SeanCline/RabidKeyboard/pcb/images/pcb-back-3d.png

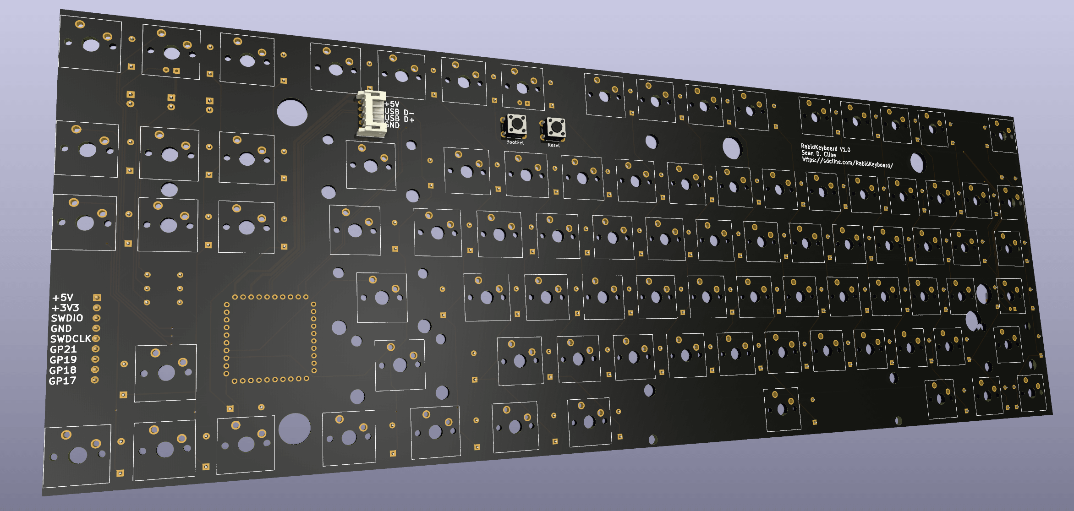
pcb/images/pcb-back-3d.png
