SeanCline/RabidKeyboard/pcb/images/pcb-back.png

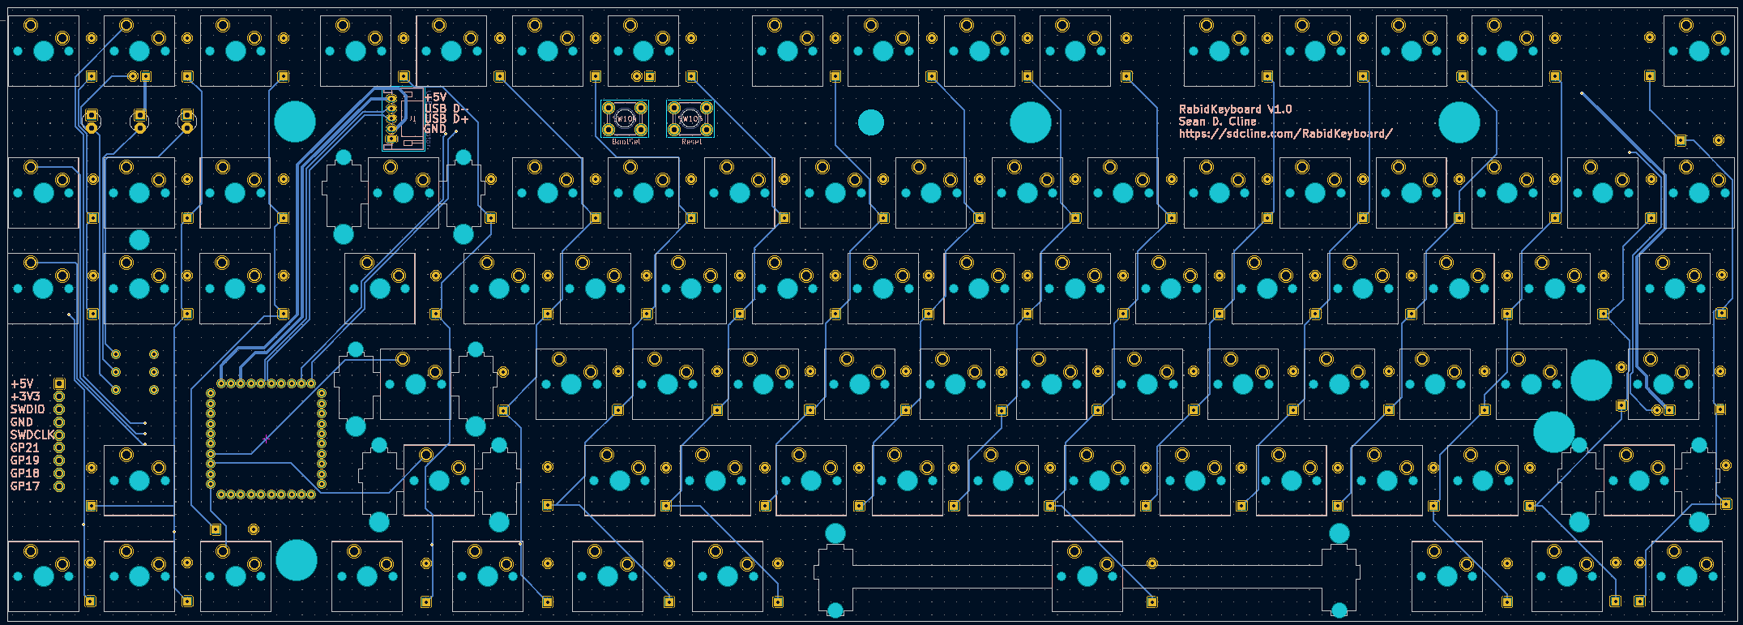
pcb/images/pcb-back.png
