SeanCline/RabidKeyboard/plate/images/plate-front.png

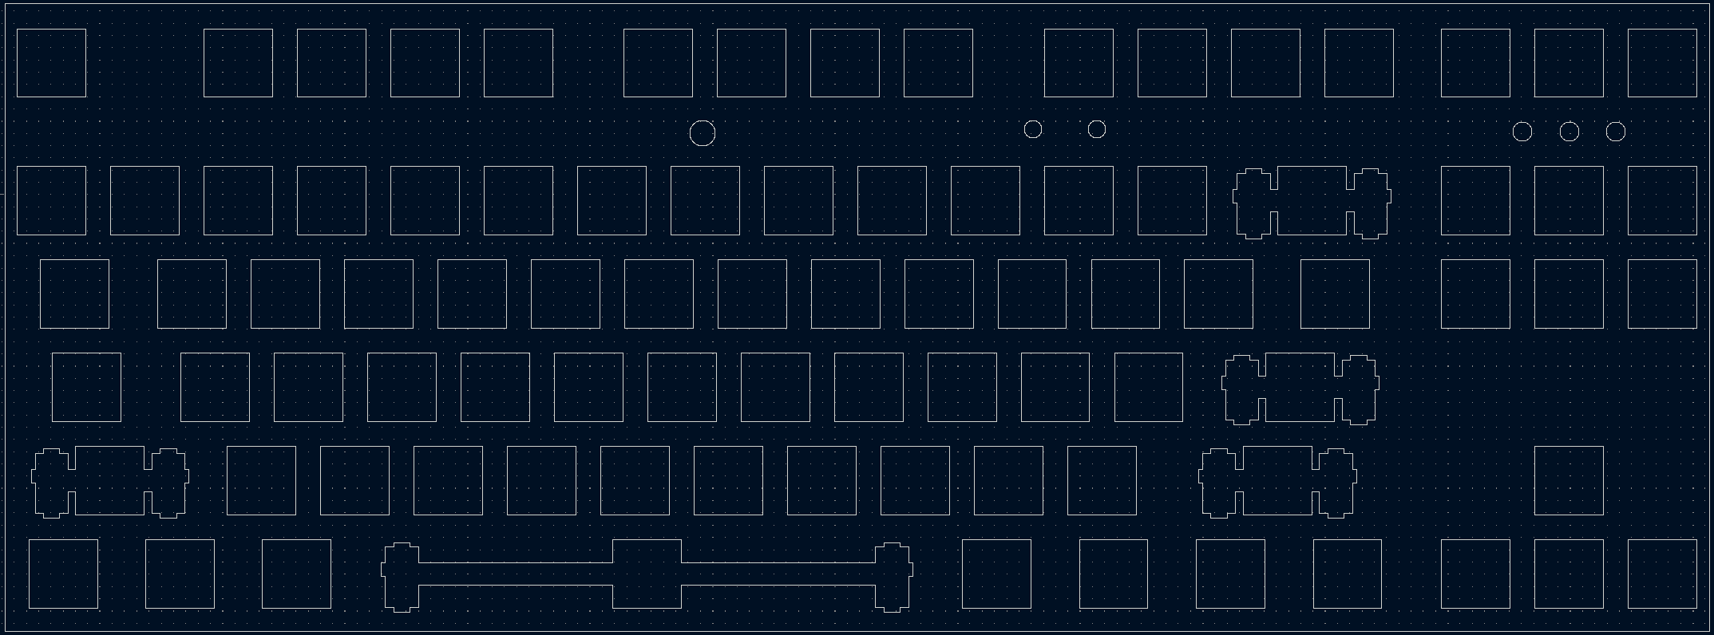
plate/images/plate-front.png
