SeanCline/RabidKeyboard/reference/Microcontrollers/pga2040.jpg

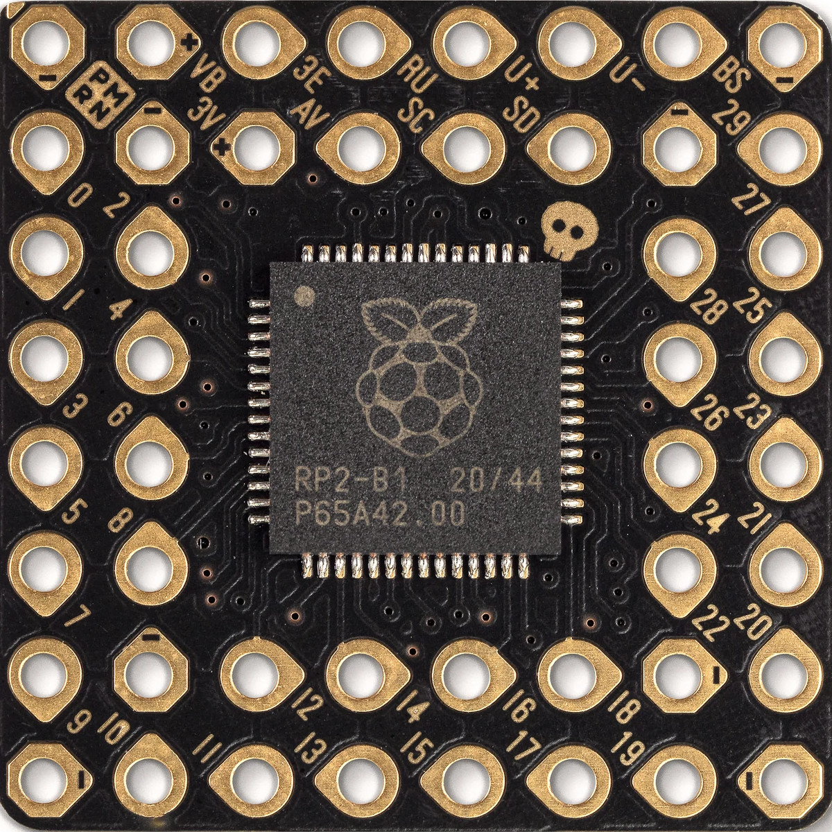
reference/Microcontrollers/pga2040.jpg
