SeanCline/RabidKeyboard/reference/Microcontrollers/pi_pico.jpg

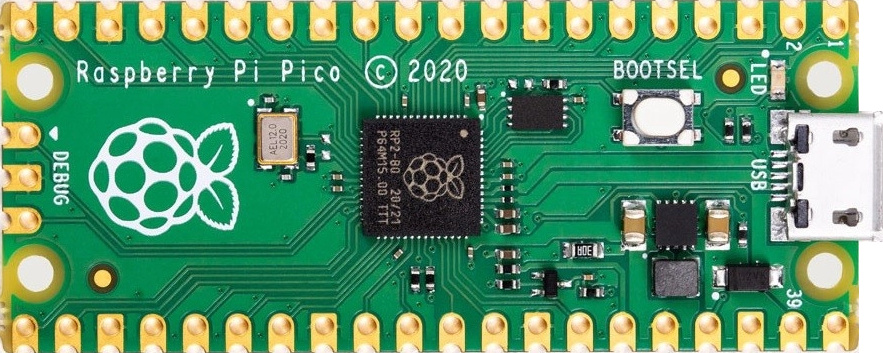
reference/Microcontrollers/pi_pico.jpg
