SeanCline/RabidKeyboard/reference/Microcontrollers/rp2040stamp.jpg

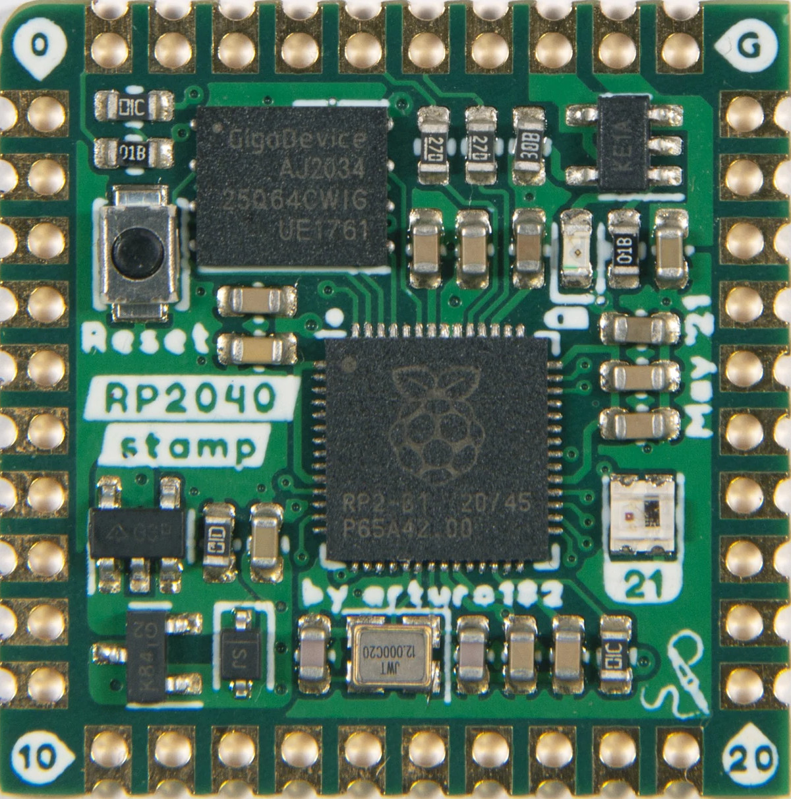
reference/Microcontrollers/rp2040stamp.jpg
