SeanCline/RabidKeyboard/reference/Quickfire Rapid/DaughterBoard - Back.png

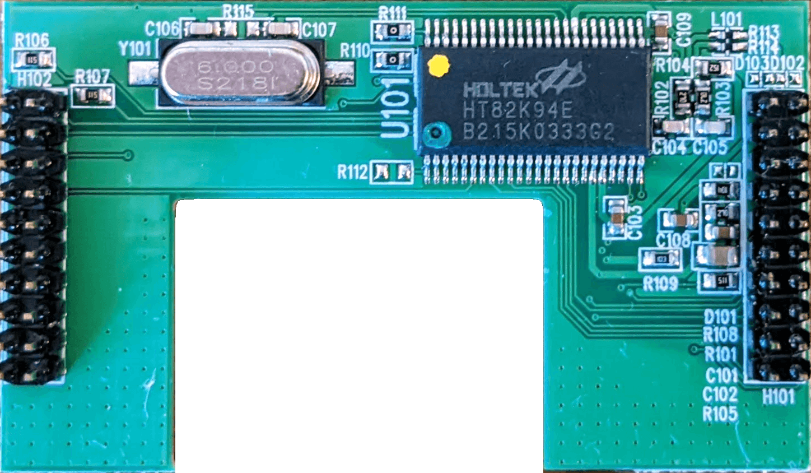
reference/Quickfire Rapid/DaughterBoard - Back.png
