SeanCline/RabidKeyboard/reference/Quickfire Rapid/DaughterBoard - Front.png

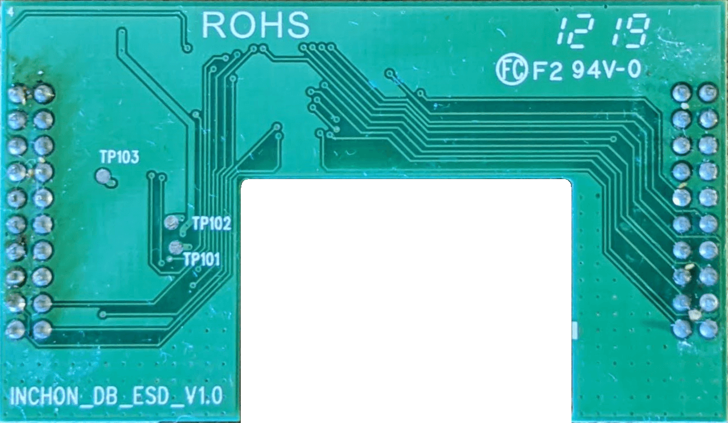
reference/Quickfire Rapid/DaughterBoard - Front.png
