SeanCline/RabidKeyboard/reference/Quickfire Rapid/PCB - Back.jpg

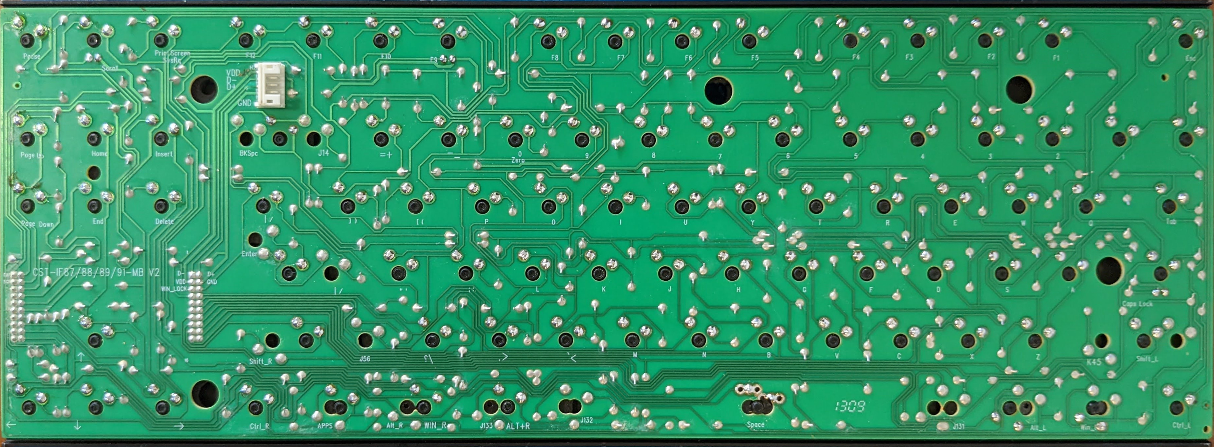
reference/Quickfire Rapid/PCB - Back.jpg
