SeanCline/RabidKeyboard/reference/Quickfire Rapid/PCB - Front.jpg

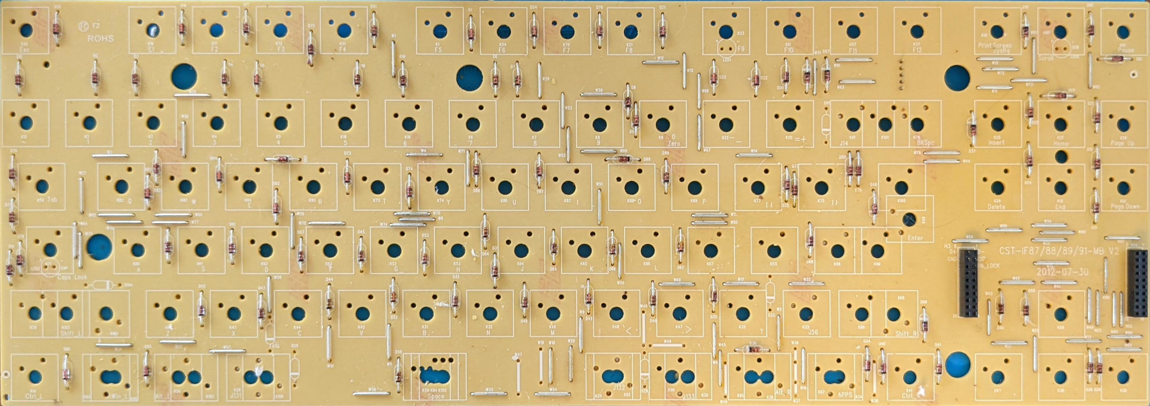
reference/Quickfire Rapid/PCB - Front.jpg
