SeanCline/RabidKeyboard/reference/Quickfire Rapid/Plate.jpg

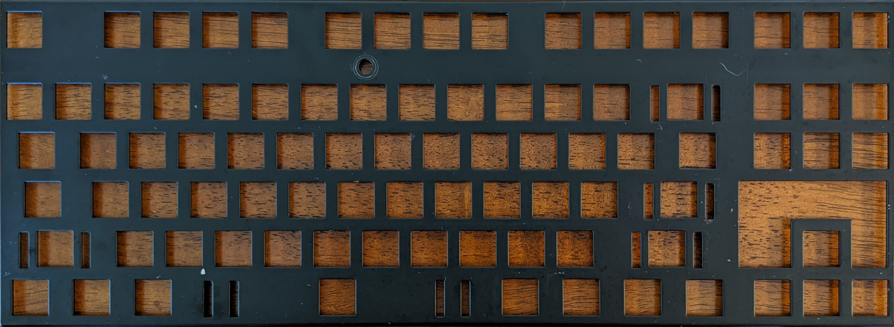
reference/Quickfire Rapid/Plate.jpg
