SeanCline/RabidKeyboard/reference/Quickfire Rapid/USB Daughterboard - Back.jpg

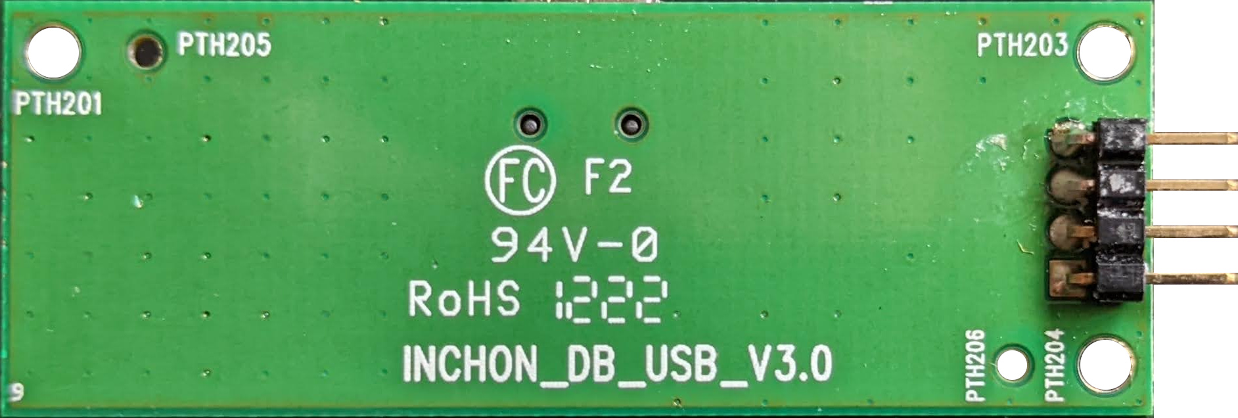
reference/Quickfire Rapid/USB Daughterboard - Back.jpg
