SeanCline/RabidKeyboard/reference/Quickfire Rapid/USB Daughterboard - Front.jpg

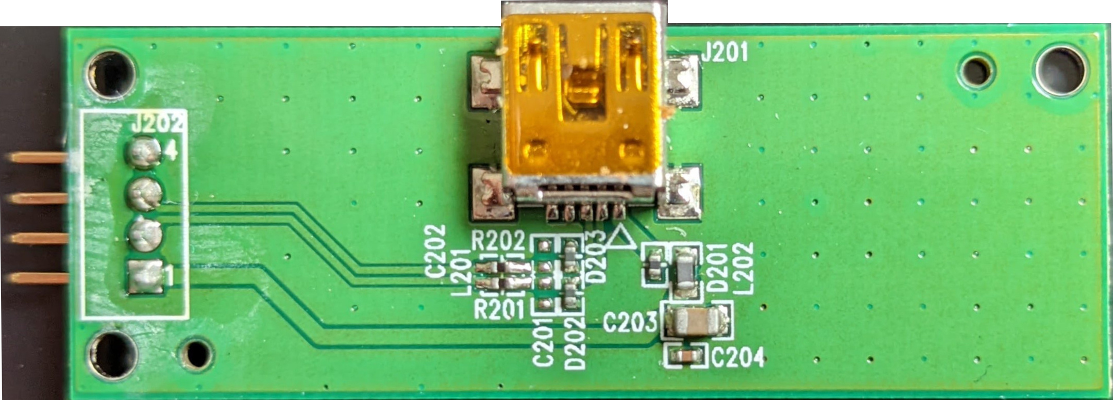
reference/Quickfire Rapid/USB Daughterboard - Front.jpg
