SeanCline/RabidKeyboard/reference/YMDK/YMDK Usb - Back.png

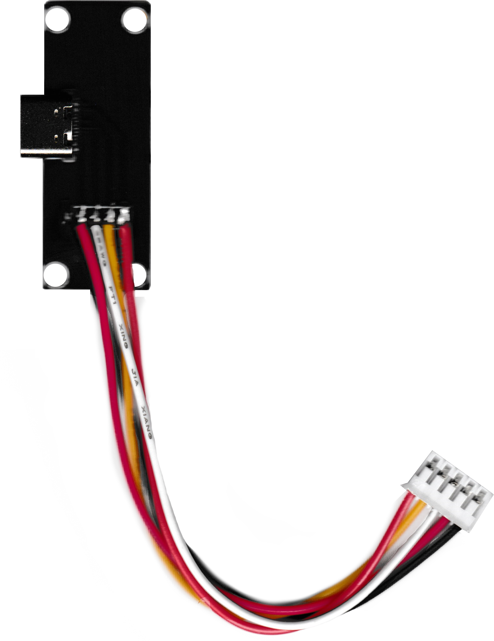
reference/YMDK/YMDK Usb - Back.png
