SeanCline/RabidKeyboard/reference/YMDK/YMDK Usb - Front.png

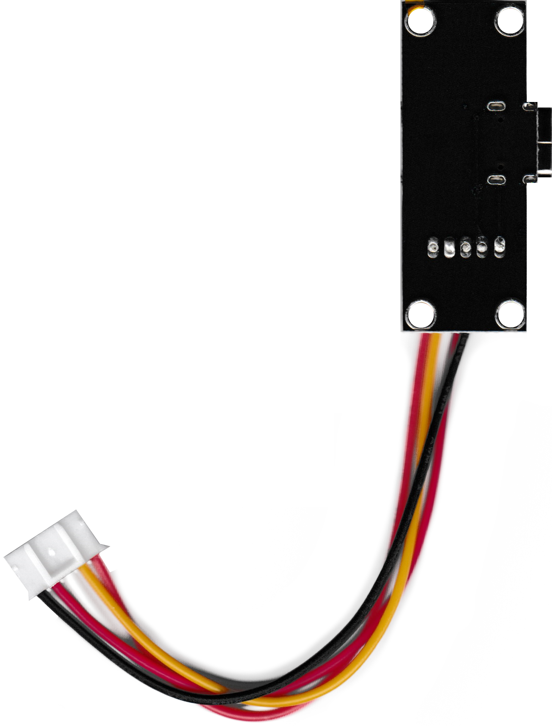
reference/YMDK/YMDK Usb - Front.png
