SeanCline/RabidKeyboard/usb_costar/gerbers/JLCPCB Production File/Produce_DanZhi.SMT_Snapshot.Top.4573307A_Y5.SMT0220727918202.png

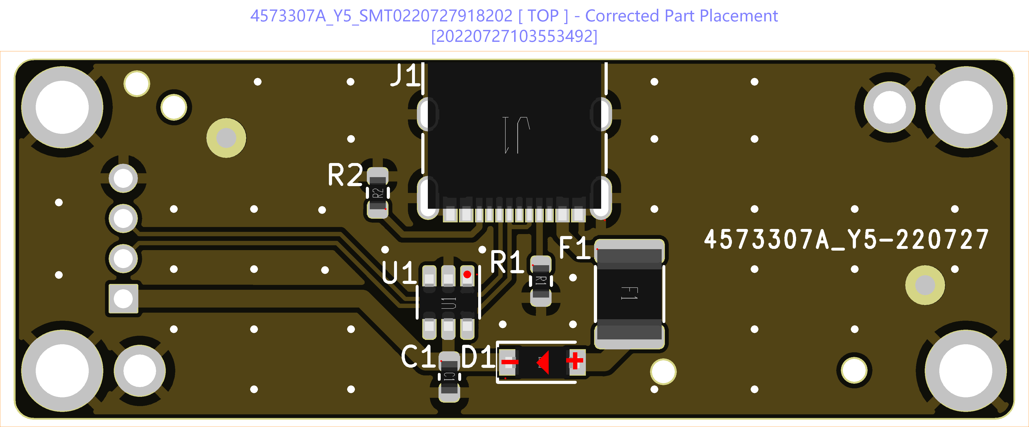
usb_costar/gerbers/JLCPCB Production File/Produce_DanZhi.SMT_Snapshot.Top.4573307A_Y5.SMT0220727918202.png
