SeanCline/RabidKeyboard/usb_costar/images/usb_costar-back.png

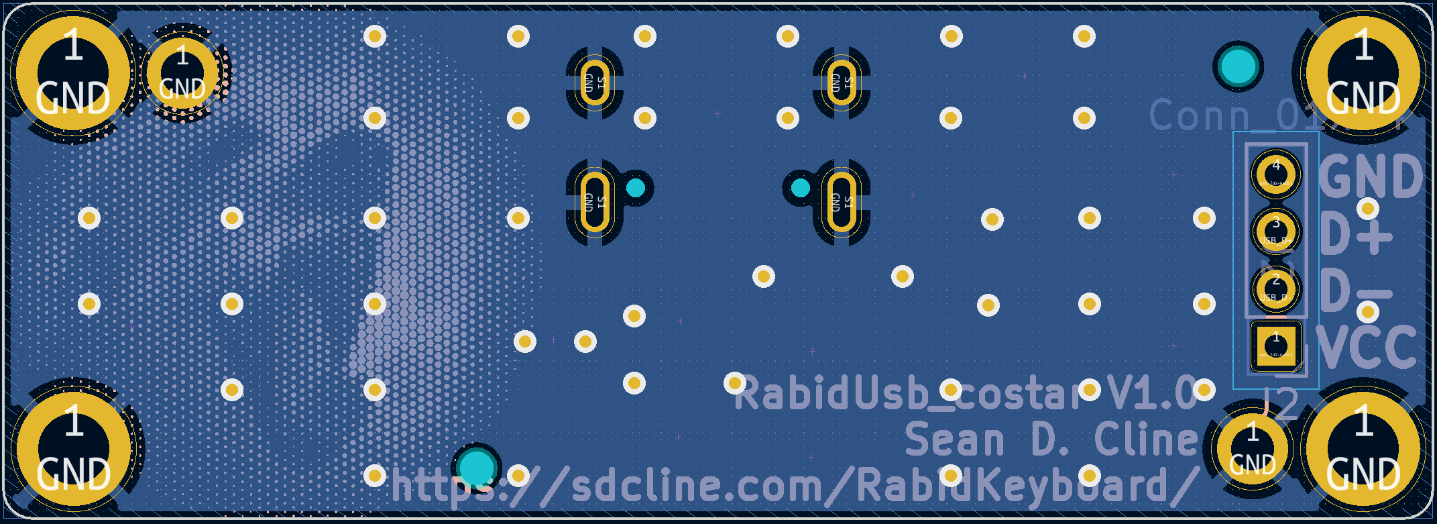
usb_costar/images/usb_costar-back.png
