SeanCline/RabidKeyboard/usb_costar/images/usb_costar-schematic.png

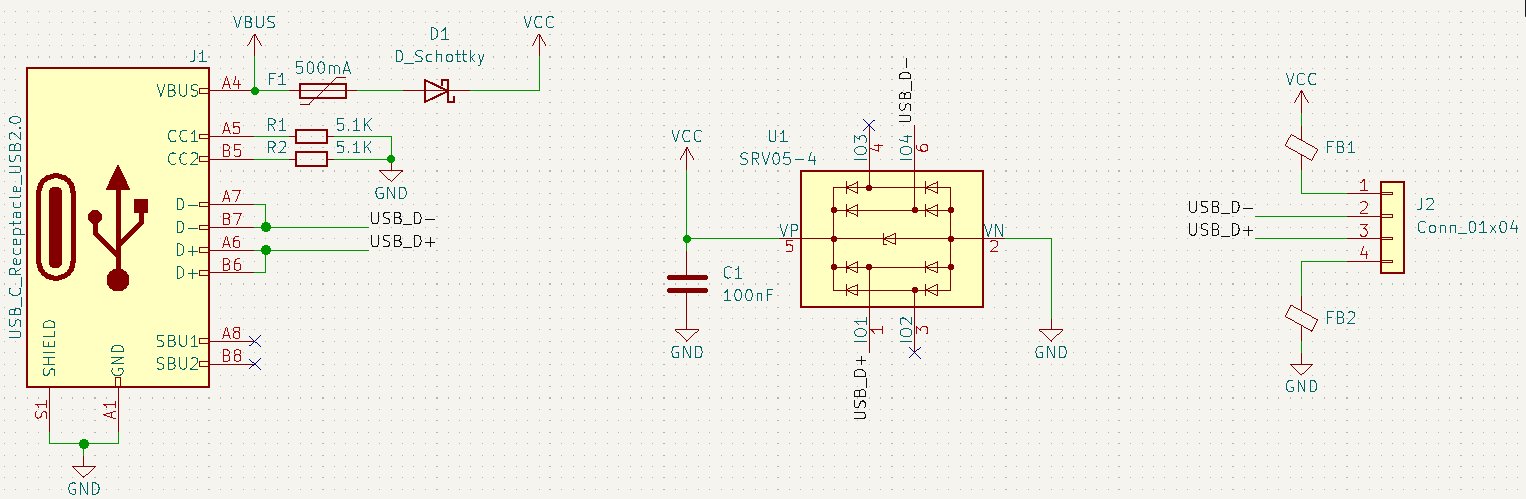
usb_costar/images/usb_costar-schematic.png
