SeanCline/RabidKeyboard/usb_ymdk/gerber/JLCPCB Production File/downloadPatchImgFile.png

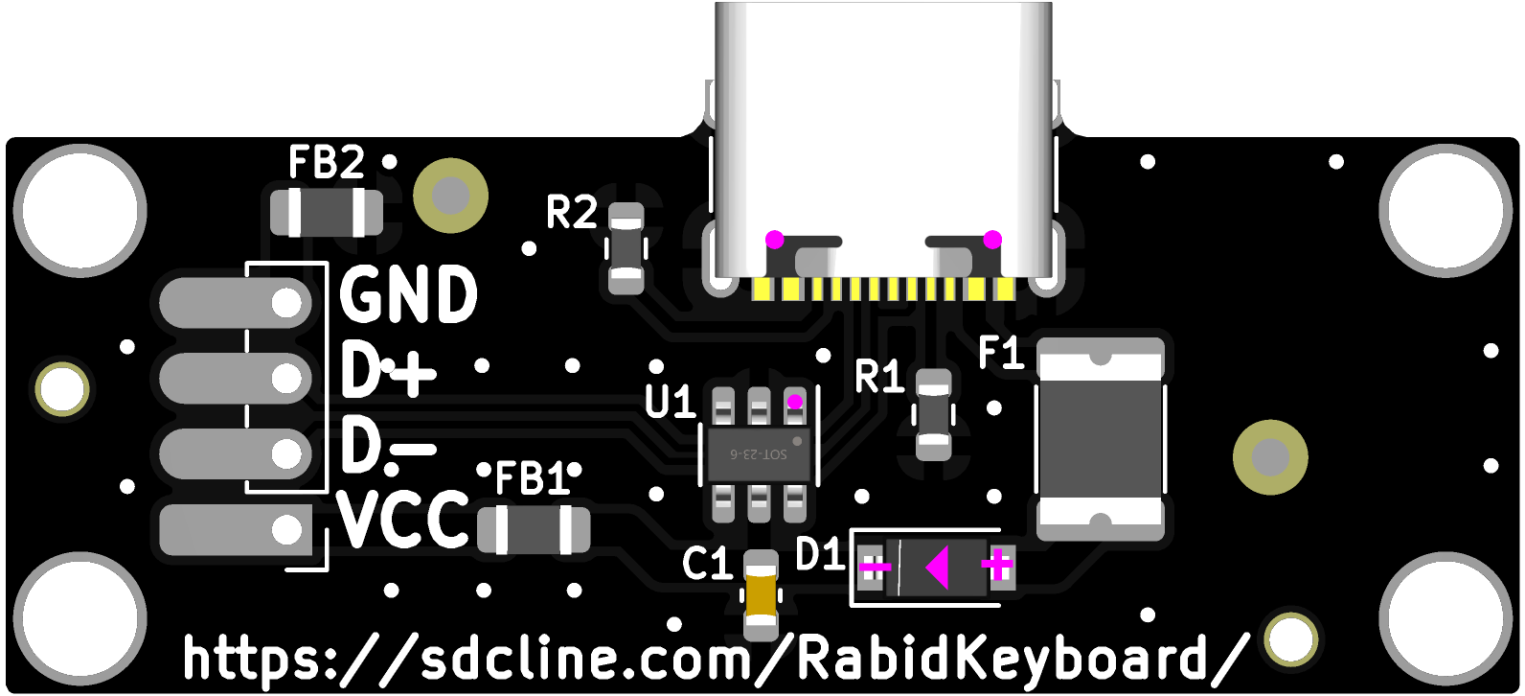
usb_ymdk/gerber/JLCPCB Production File/downloadPatchImgFile.png
