SeanCline/RabidKeyboard/usb_ymdk/gerber/JLCPCB Production File/jlcNAV6FVA5SPOBbottom-4480x3200.png

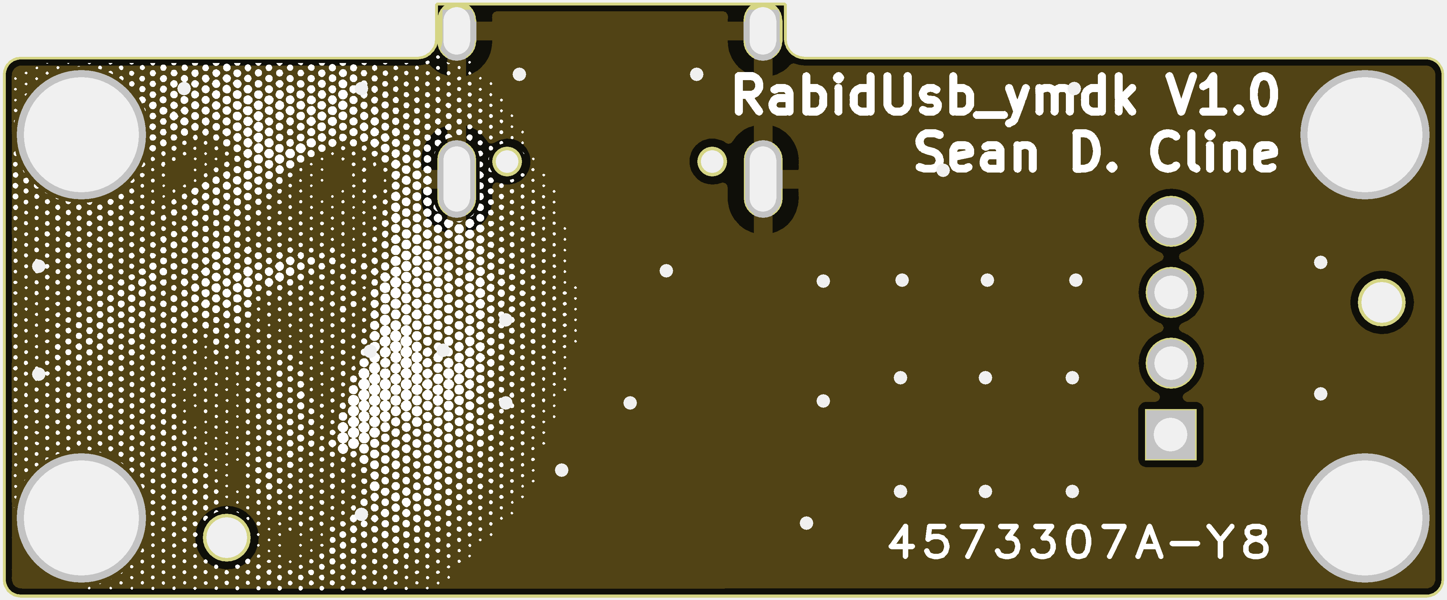
usb_ymdk/gerber/JLCPCB Production File/jlcNAV6FVA5SPOBbottom-4480x3200.png
