SeanCline/RabidKeyboard/usb_ymdk/gerber/JLCPCB Production File/jlcNAV6FVA5SPOBtop-4480x3200.png

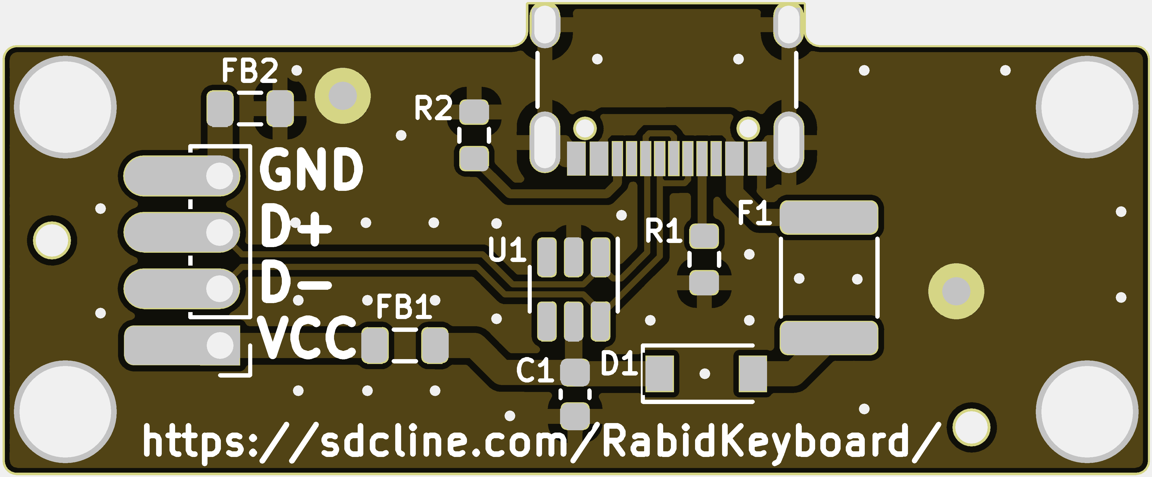
usb_ymdk/gerber/JLCPCB Production File/jlcNAV6FVA5SPOBtop-4480x3200.png
