SeanCline/RabidKeyboard/usb_ymdk/gerber/JLCPCB Production File/Produce_DanZhi.SMT_Original_Snapshot.Top.4573307A_Y8.SMT0220829947401.png

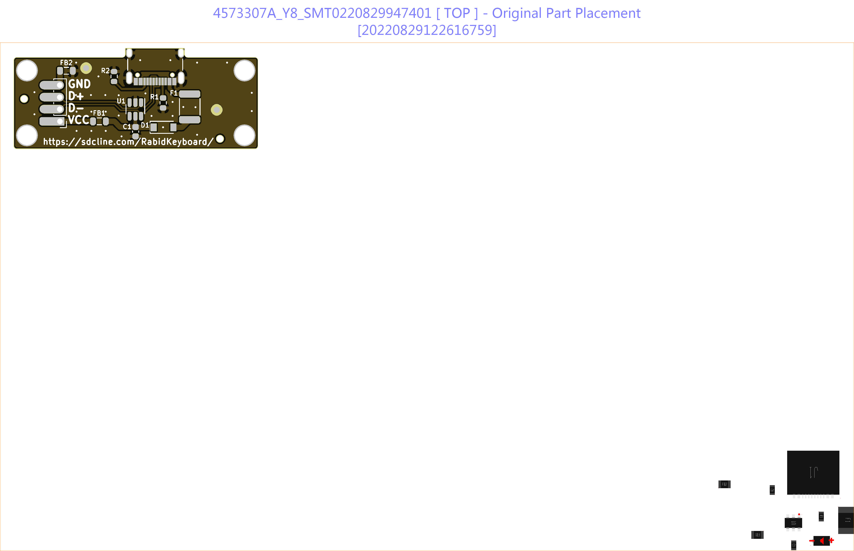
usb_ymdk/gerber/JLCPCB Production File/Produce_DanZhi.SMT_Original_Snapshot.Top.4573307A_Y8.SMT0220829947401.png
