SeanCline/RabidKeyboard/usb_ymdk/images/usb_ymdk-back.png

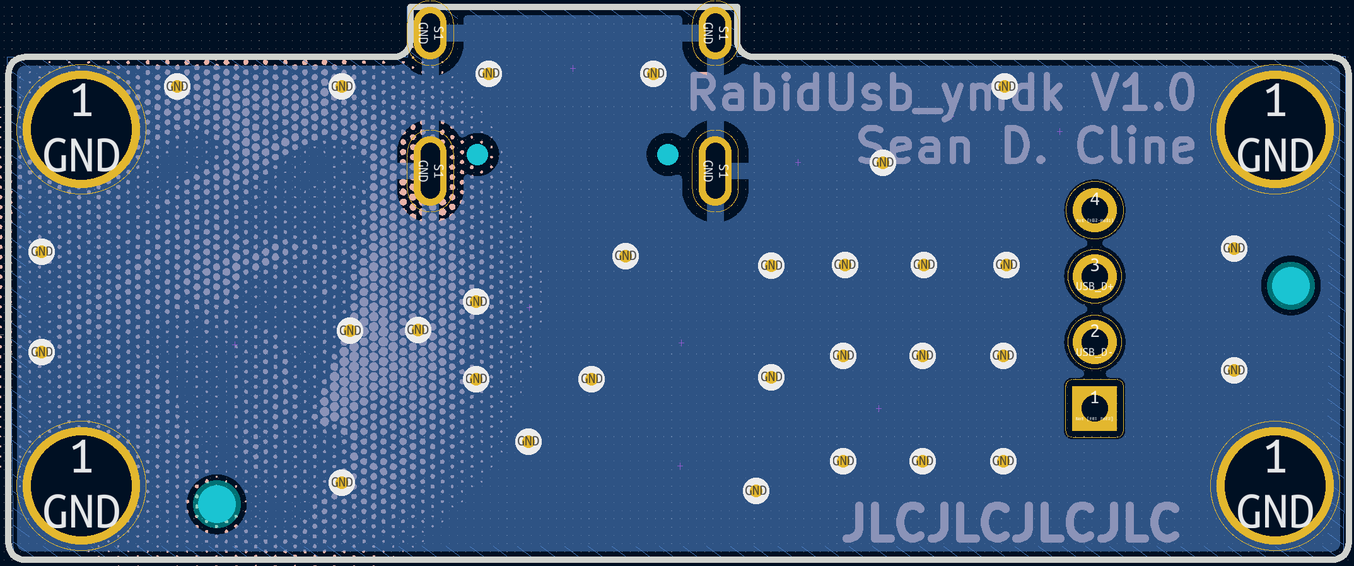
usb_ymdk/images/usb_ymdk-back.png
