SeanCline/RabidKeyboard/reference/YMDK/YMDK Usb - Measurements.jpg

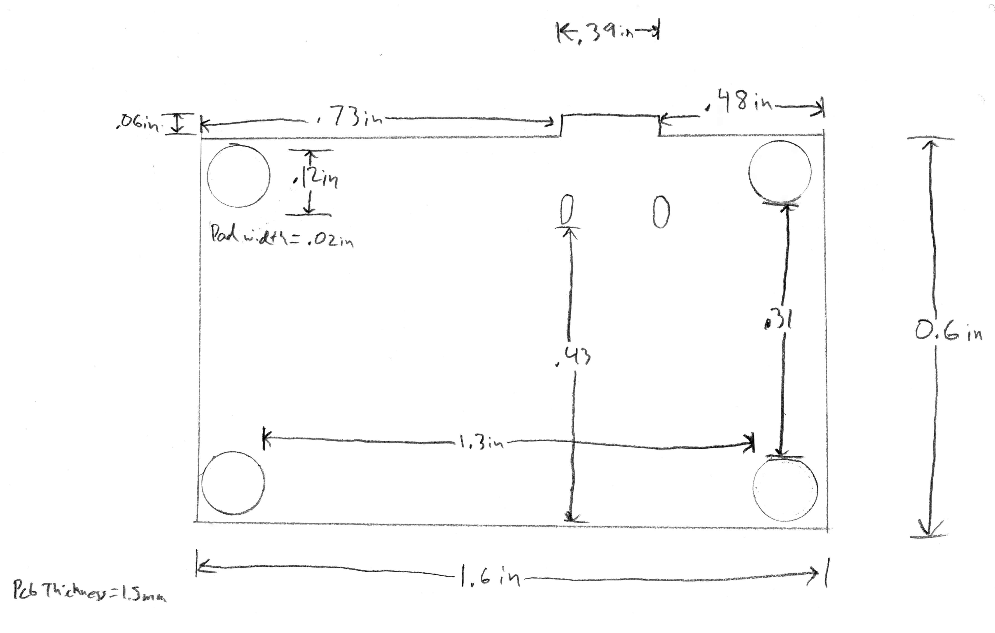
reference/YMDK/YMDK Usb - Measurements.jpg
